capracreations/Coolest-Laptop-Cooler/Temperature_data/temperature_graphs/blops6_laptopfans.png

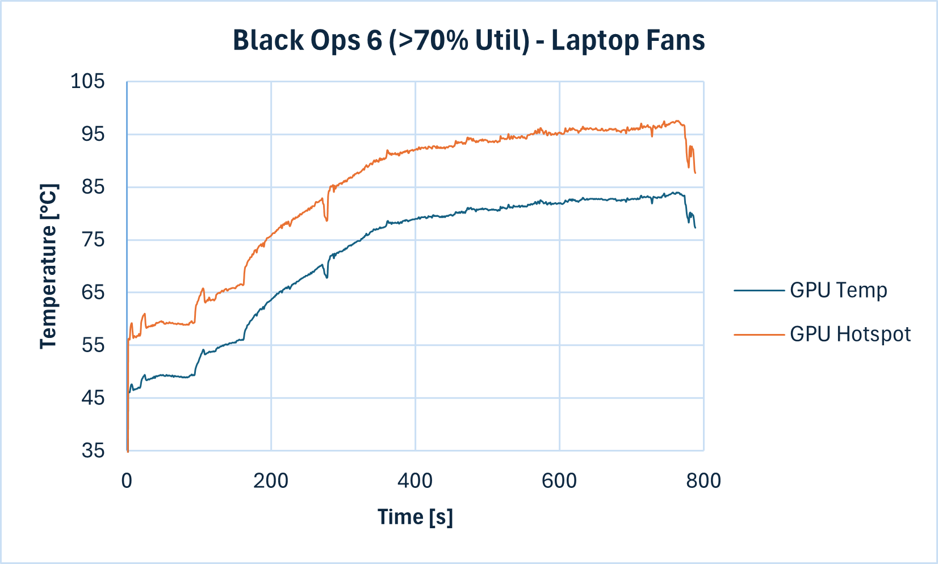
Temperature_data/temperature_graphs/blops6_laptopfans.png
