capracreations/Coolest-Laptop-Cooler/Temperature_data/temperature_graphs/Cyberpunk2077_allfans.png

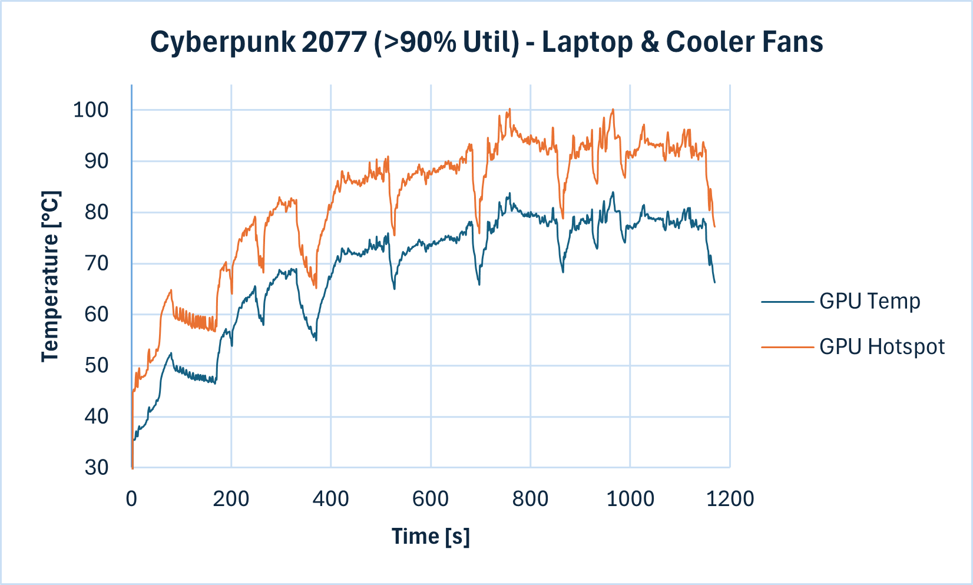
Temperature_data/temperature_graphs/Cyberpunk2077_allfans.png
