capracreations/Coolest-Laptop-Cooler/Temperature_data/temperature_graphs/EldenRing_allfans.png

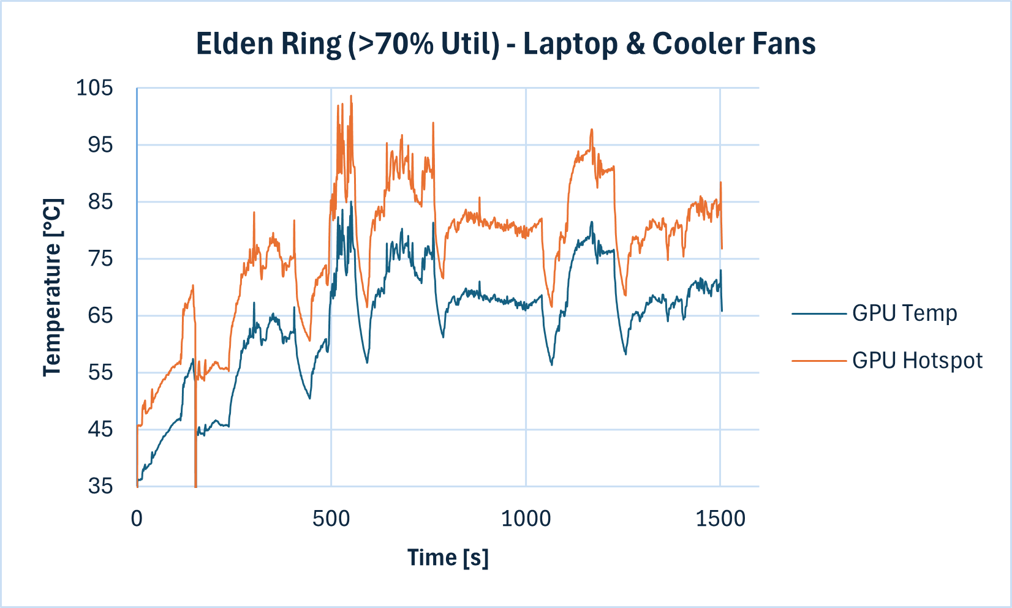
Temperature_data/temperature_graphs/EldenRing_allfans.png
