capracreations/Coolest-Laptop-Cooler/Temperature_data/temperature_graphs/Witcher3_allfans.png

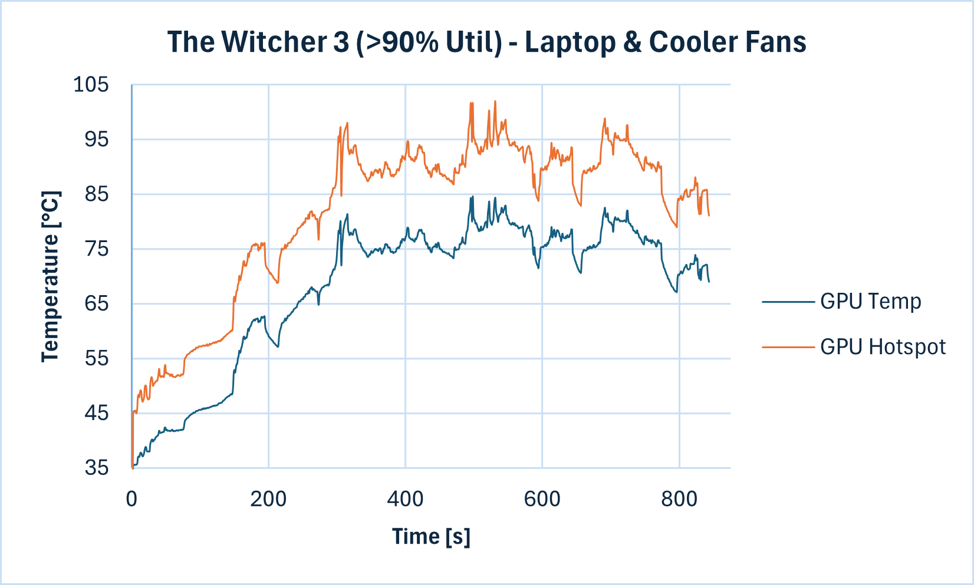
Temperature_data/temperature_graphs/Witcher3_allfans.png
